wware/instrument2015/boards/Instrument2015.png

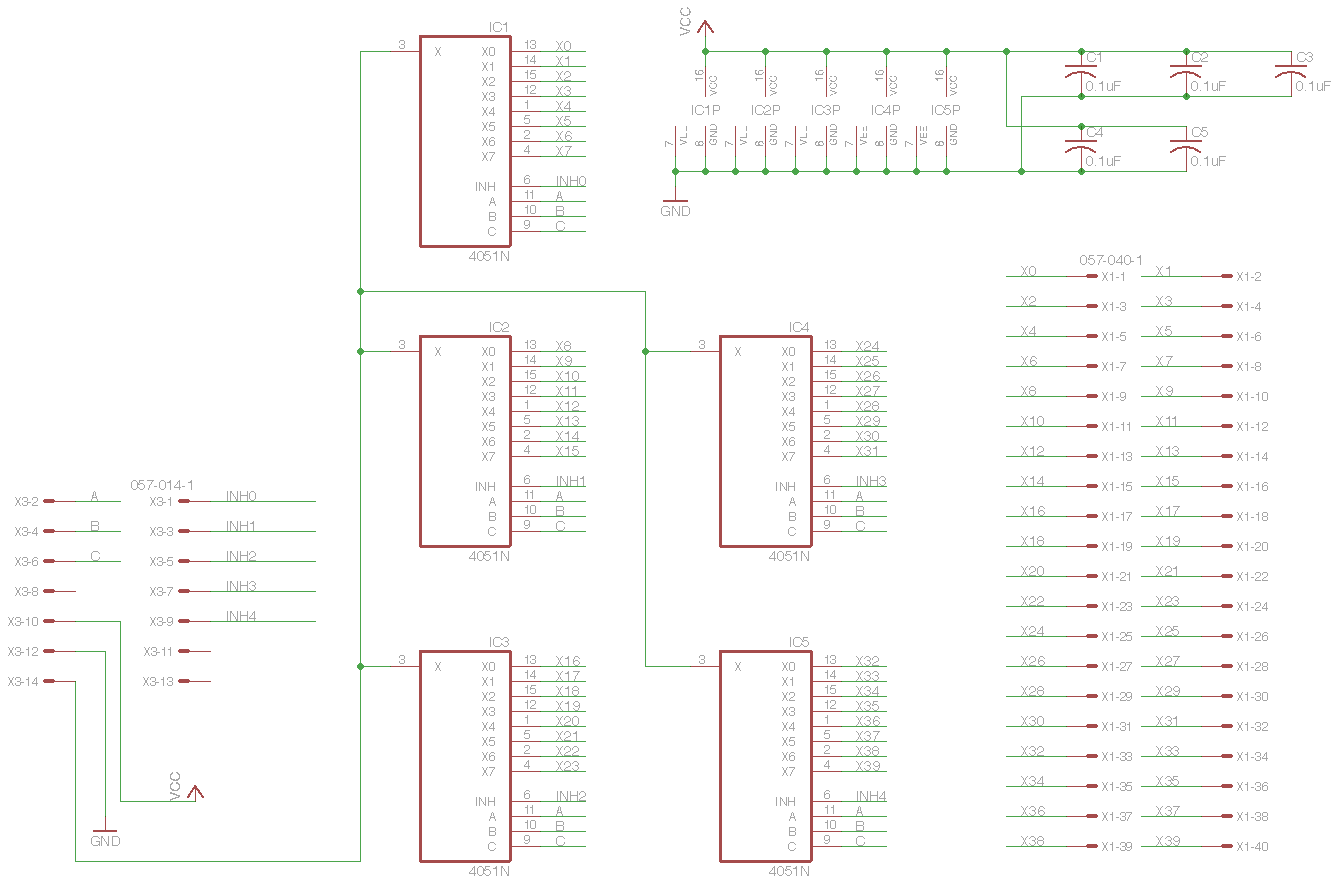
boards/Instrument2015.png
